idorurez/SSD1326_I2C_breakout/datasheet/ER-CON26HT-1.png

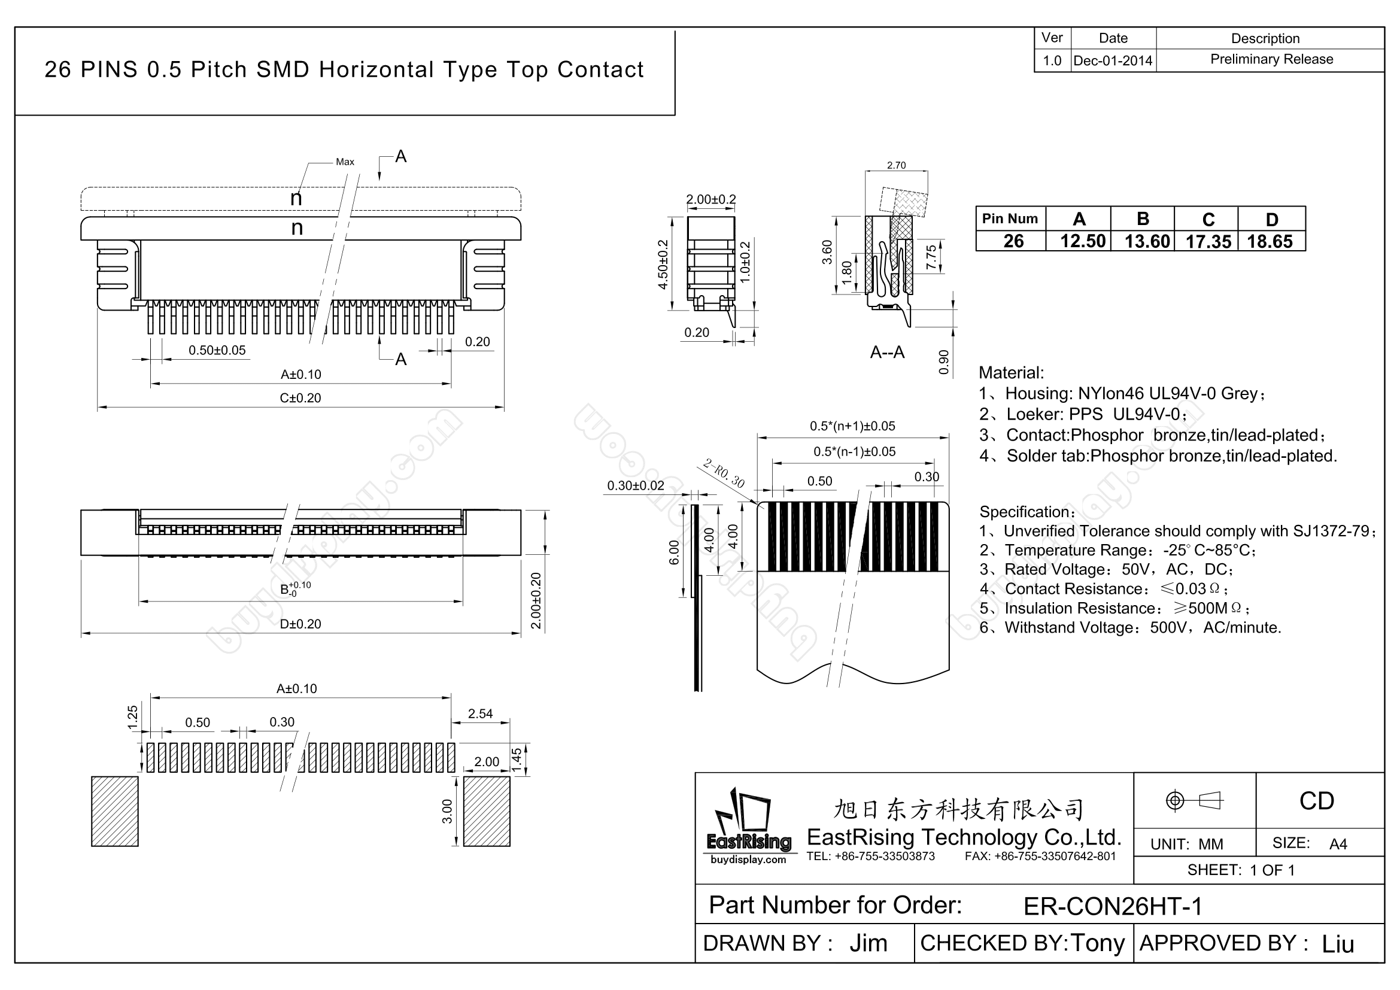
datasheet/ER-CON26HT-1.png
