idorurez/SSD1326_I2C_breakout/datasheet/ER-OLED018-1_Series_Datasheet/ER-OLED018-1_Series_Datasheet-04.png

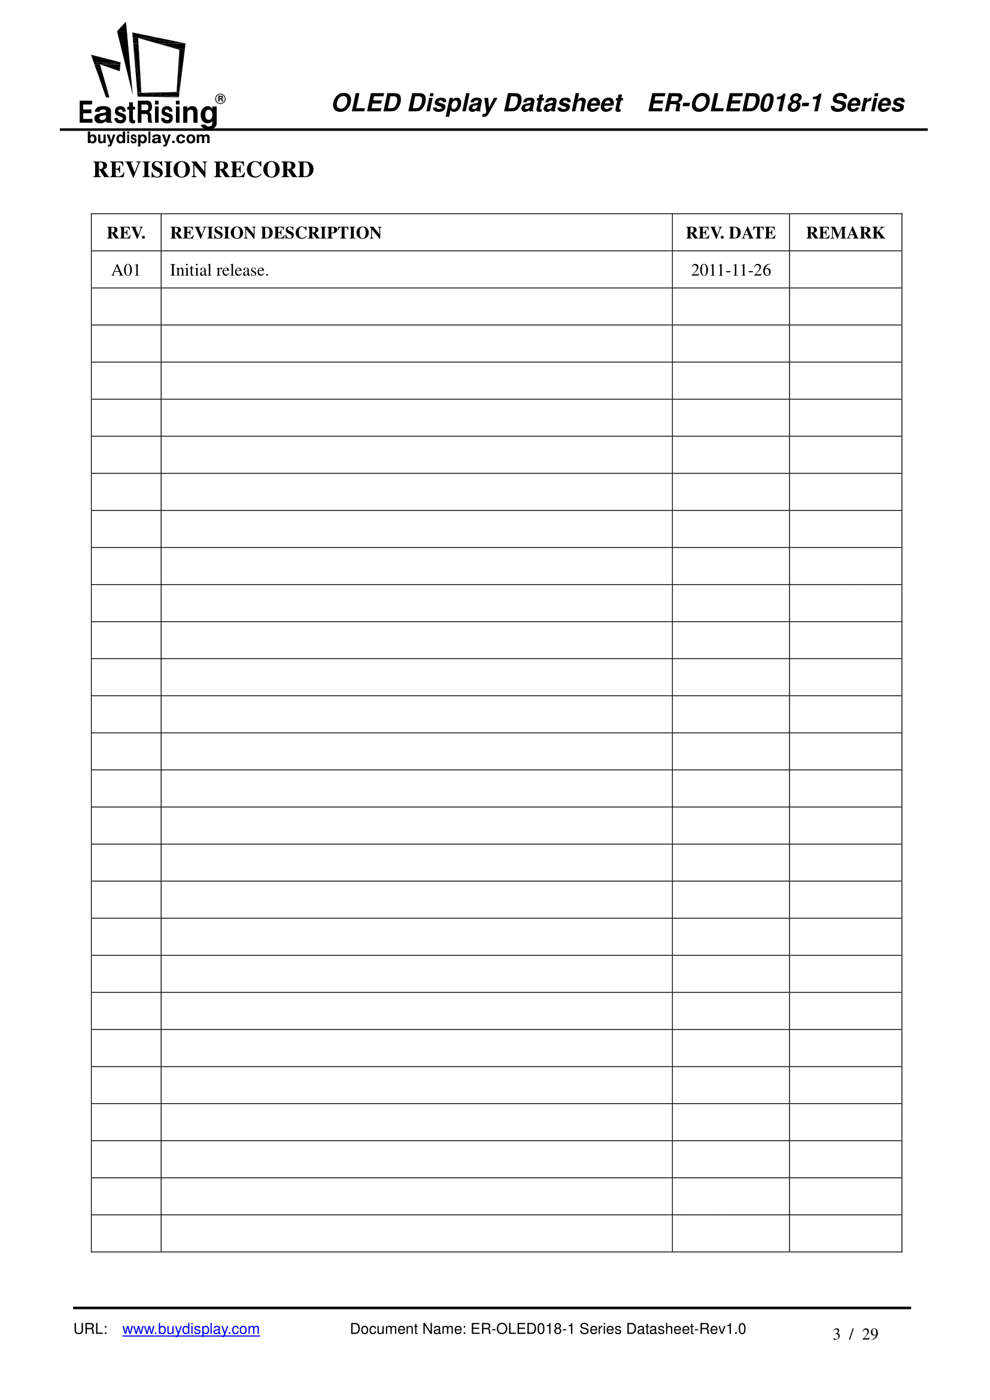
datasheet/ER-OLED018-1_Series_Datasheet/ER-OLED018-1_Series_Datasheet-04.png
